StevenConnors/Filloaster/bootstrap/css/prototype1.jpg

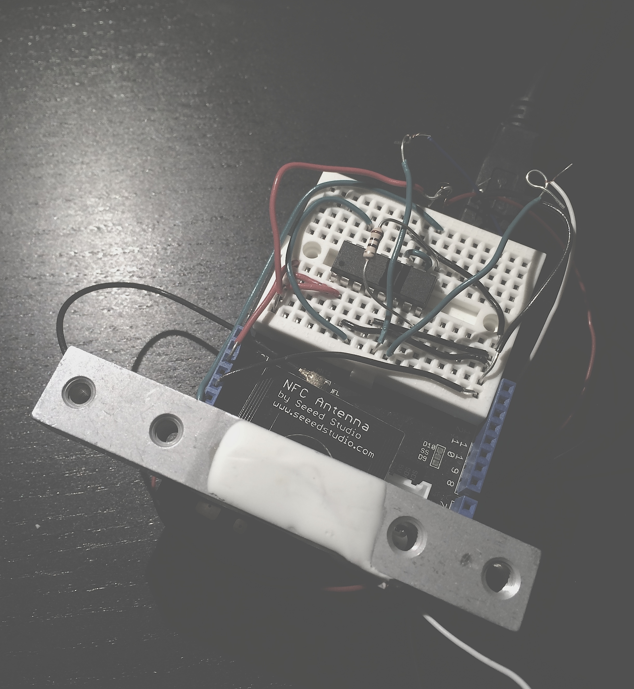
bootstrap/css/prototype1.jpg
