StevenConnors/Filloaster/documents/Filloaster_Diagram.png

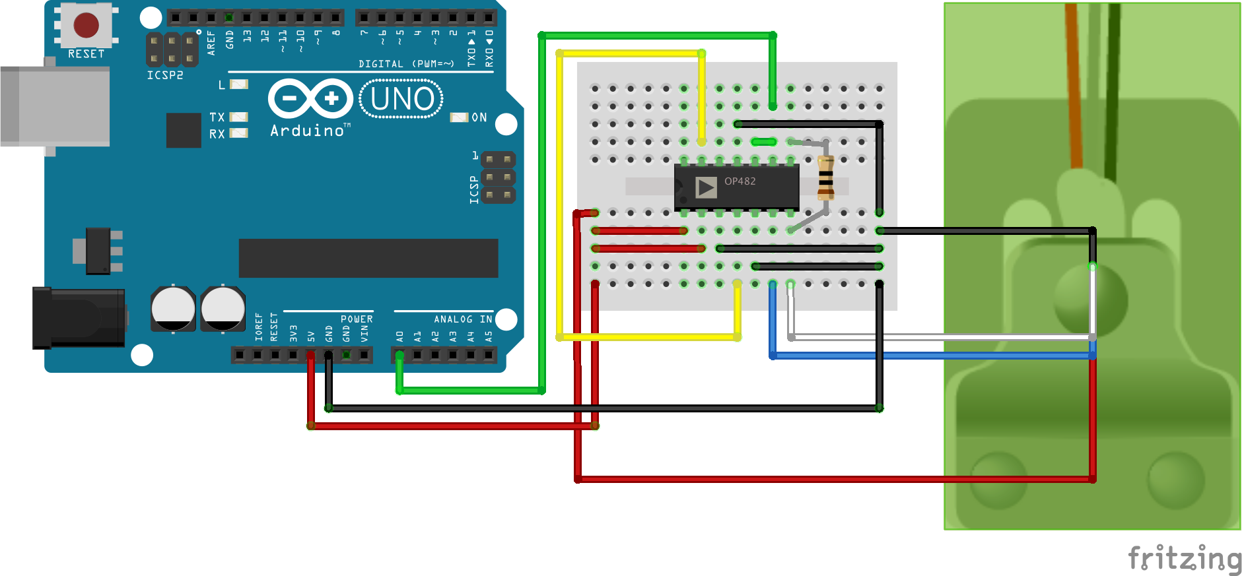
documents/Filloaster_Diagram.png
