StevenConnors/Filloaster/Documents/Photos/IMG_3667.JPG

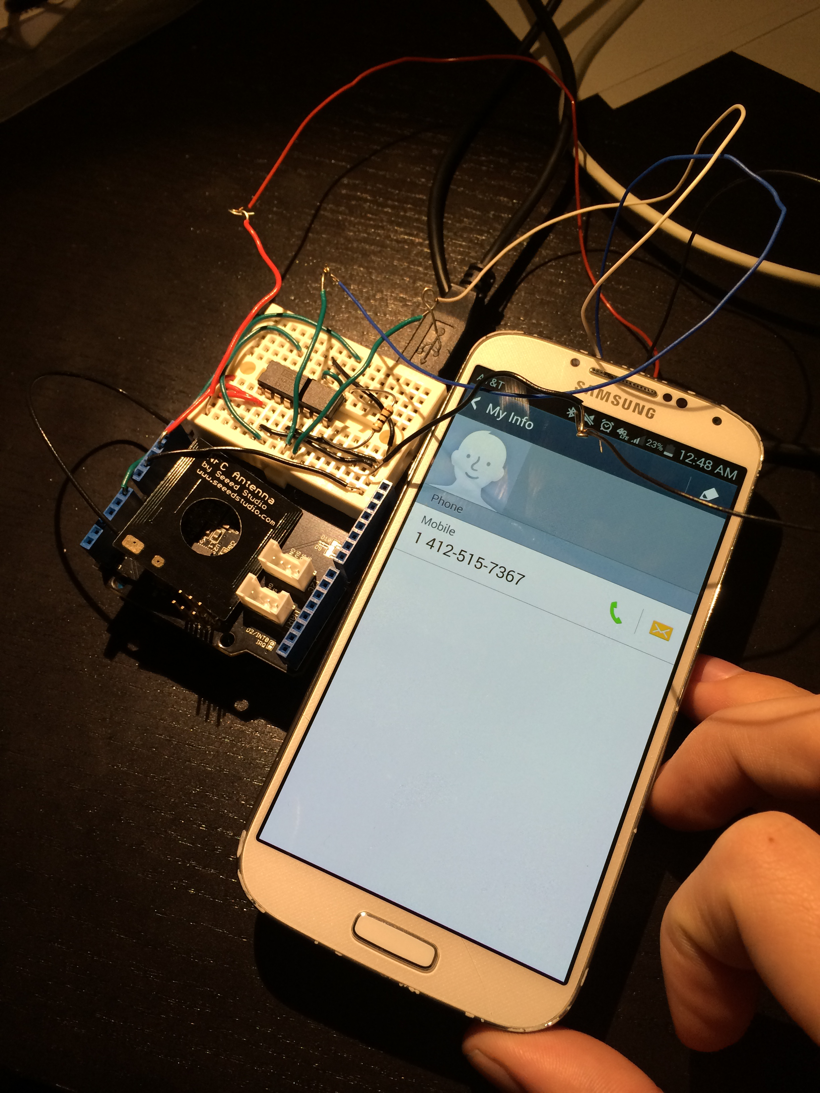
Documents/Photos/IMG_3667.JPG
