StevenConnors/Filloaster/documents/photos/prototype2.jpg

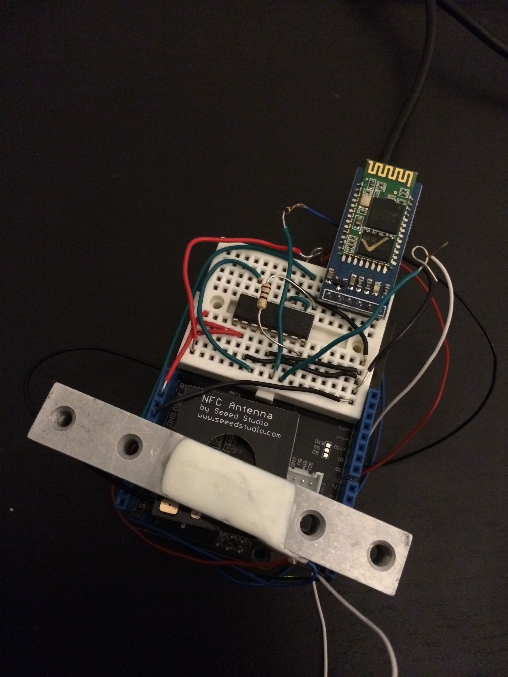
documents/photos/prototype2.jpg
