StevenConnors/Filloaster/Documents/Photos/Screen Shot 2014-12-03 at 1.07.31 AM.png

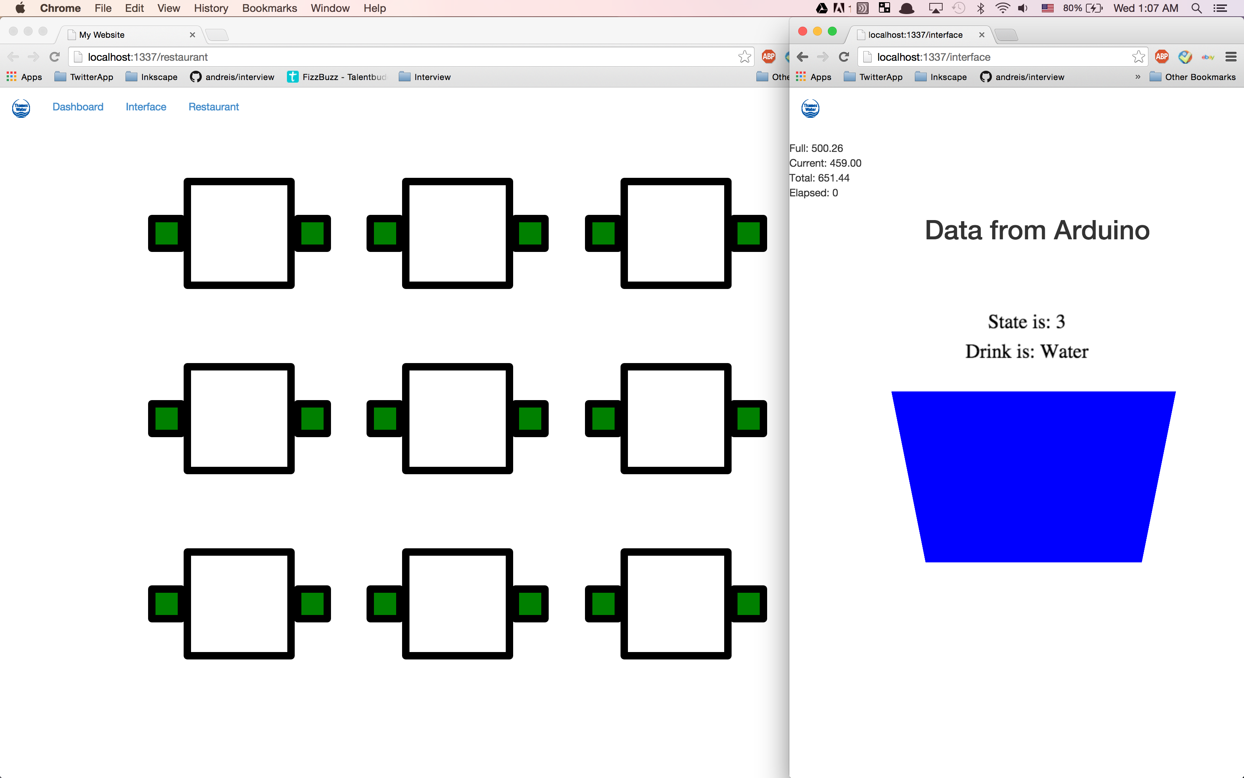
Documents/Photos/Screen Shot 2014-12-03 at 1.07.31 AM.png
