StevenConnors/Filloaster/Documents/Photos/Screen Shot 2014-12-03 at 12.55.36 AM.png

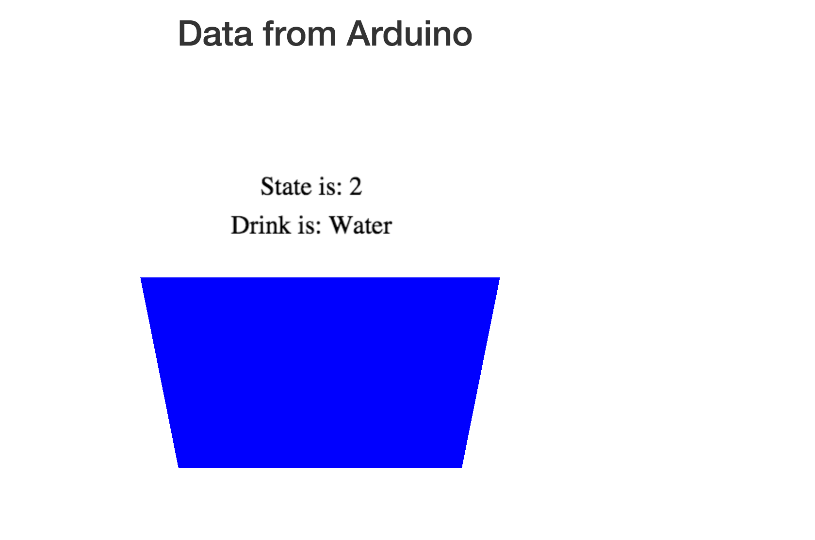
Documents/Photos/Screen Shot 2014-12-03 at 12.55.36 AM.png
