StevenConnors/Filloaster/Documents/Photos/Screenshot_2014-12-03-00-50-06.png

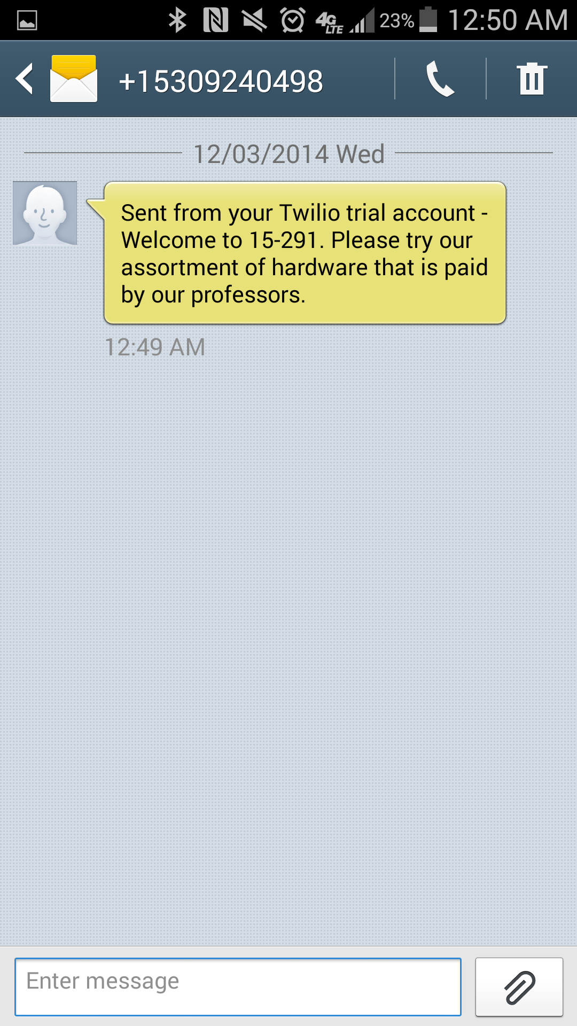
Documents/Photos/Screenshot_2014-12-03-00-50-06.png
