StevenConnors/Filloaster/Documents/Photos/Screenshot_2014-12-03-00-56-17.png

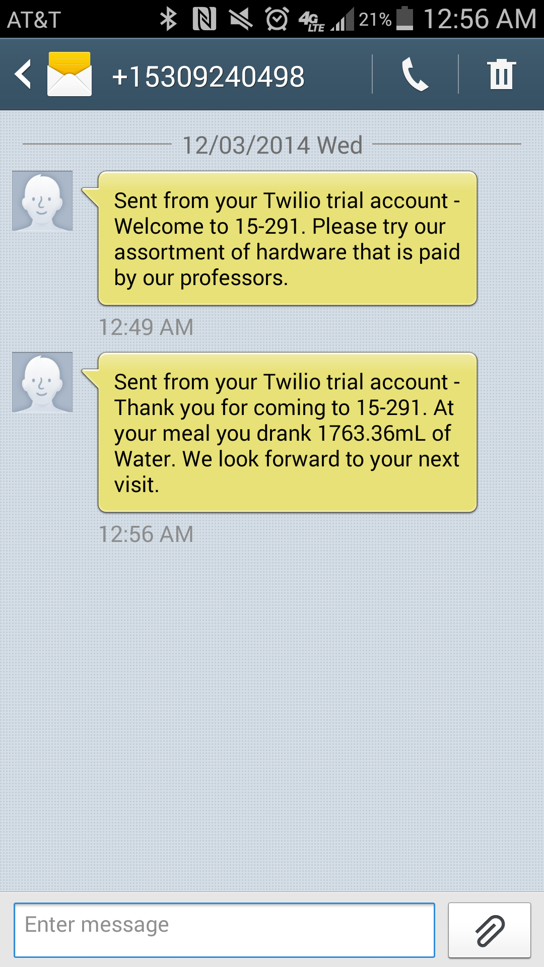
Documents/Photos/Screenshot_2014-12-03-00-56-17.png
