StevenConnors/Filloaster/Documents/Photos/Screenshot_2014-12-03-04-07-49.png

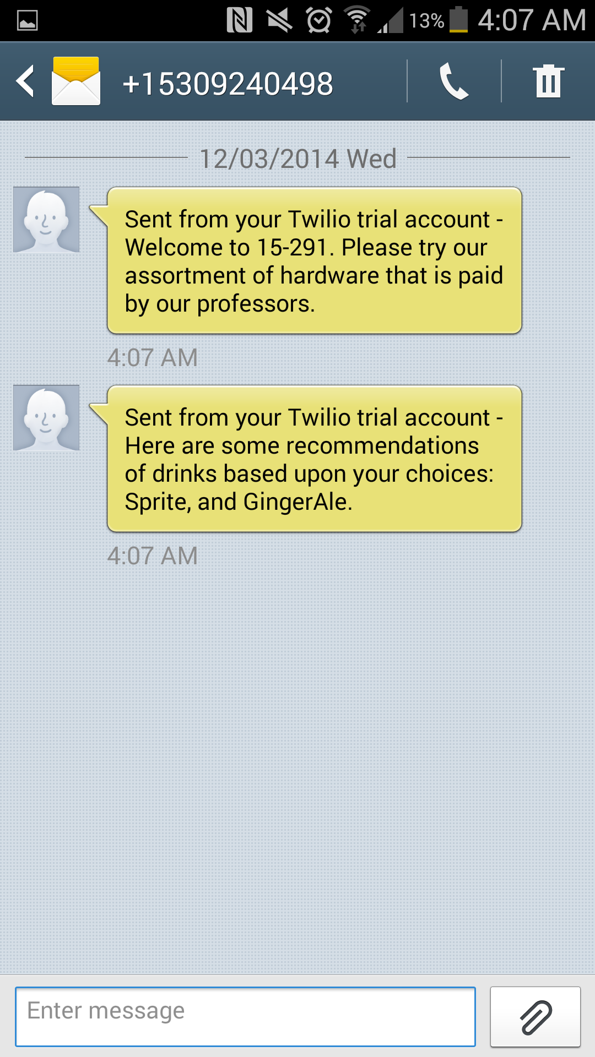
Documents/Photos/Screenshot_2014-12-03-04-07-49.png
