StevenConnors/Filloaster/documents/photos/Screenshot_2014-12-03-18-01-13.png

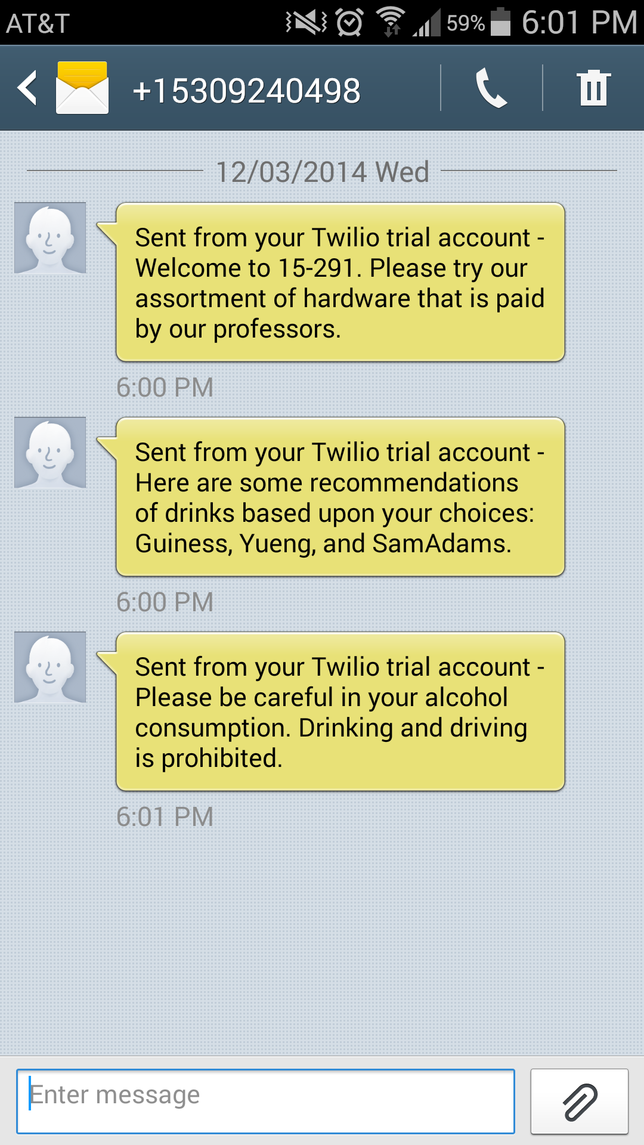
documents/photos/Screenshot_2014-12-03-18-01-13.png
